uncookednehuel/TrumpetTuner/photos/3D print of the final case.jpg

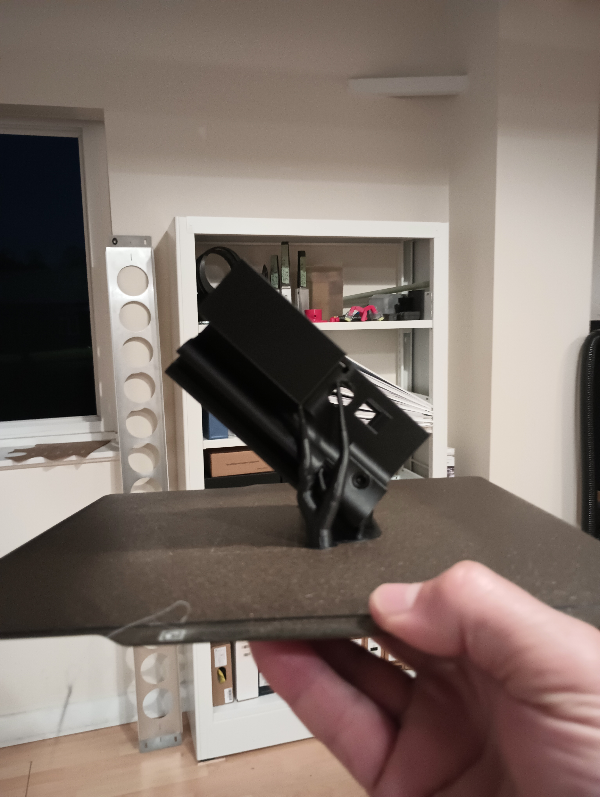
photos/3D print of the final case.jpg
