uncookednehuel/TrumpetTuner/photos/Final assembly, missing controls board bolts.jpg

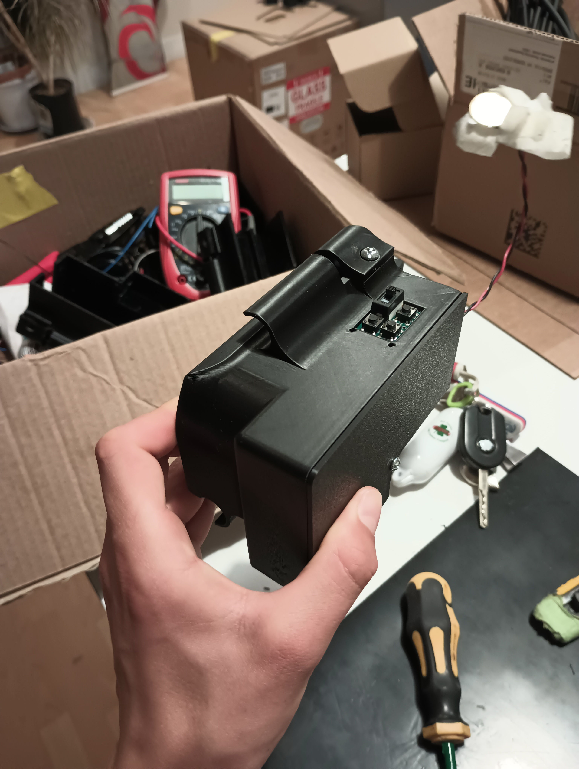
photos/Final assembly, missing controls board bolts.jpg
