uncookednehuel/TrumpetTuner/photos/First electronics install.jpg

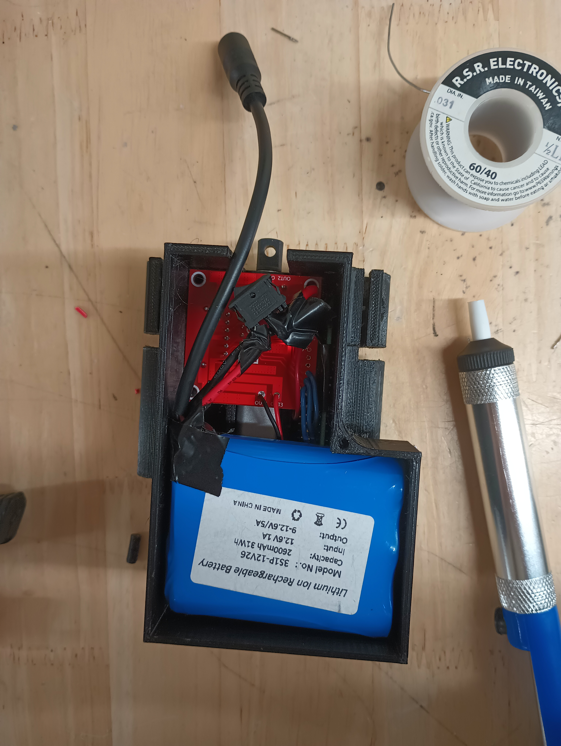
photos/First electronics install.jpg
